701Enti/SEVETEST30/pattern/IMG20230719233832.jpg

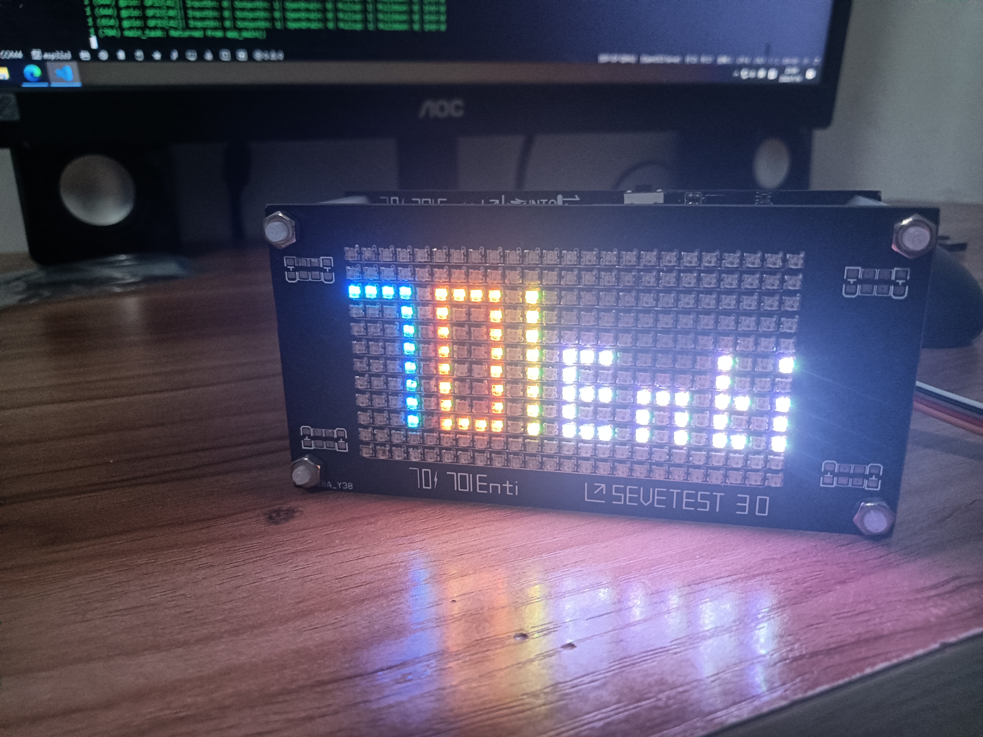
pattern/IMG20230719233832.jpg
