701Enti/SEVETEST30/pattern/sign/sign_sevetest30.png

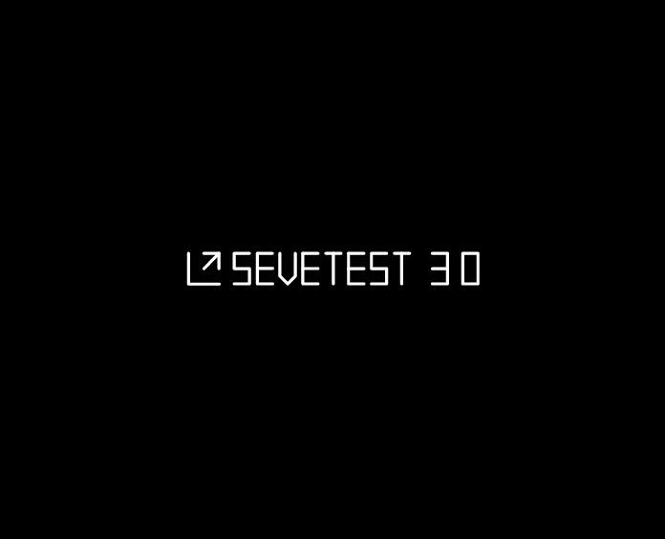
pattern/sign/sign_sevetest30.png
