701Enti/SEVETEST30/main/include/sevetest30_UI.h

/*
 * 701Enti MIT License
 *
 * Copyright © 2024 <701Enti organization>
 *
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
 * THE SOFTWARE IS PROVIDED “AS IS”, WITHOUT WARRANTY OF ANY KIND, EXPRESS OR
 * IMPLIED, INCLUDING BUT NOT LIMITED TO THE WARRANTIES OF MERCHANTABILITY,
 * FITNESS FOR A PARTICULAR PURPOSE AND NONINFRINGEMENT. IN NO EVENT SHALL THE
 * AUTHORS OR COPYRIGHT HOLDERS BE LIABLE FOR ANY CLAIM, DAMAGES OR OTHER
 * LIABILITY, WHETHER IN AN ACTION OF CONTRACT, TORT OR OTHERWISE, ARISING FROM,
 * OUT OF OR IN CONNECTION WITH THE SOFTWARE OR THE USE OR OTHER DEALINGS IN THE
 * SOFTWARE.
 */

// 包含对传感器数据，网络API等数据的 整理显示与动画交互工作
// 如您发现一些问题，请及时联系我们，我们非常感谢您的支持
// 敬告：该库自动调用 IWEDA库 SWEDA库 BWEDA库
// 读取数据，无需任何干涉，因此需要依赖一些库获取缓存变量，图像数据将只在文件函数内生效来节省内存，不会声明
// 显示UI根据sevetest30实际定制，特别是图像坐标，如果需要改变屏幕大小，建议自行设计修改
// github: https://github.com/701Enti

#pragma once

#include <driver/i2s.h>
#include <esp_err.h>
#include <stdbool.h>


// FFT相关
#define FFT_UI_TASK_CORE (0)              // FFT UI绘制任务核心
#define FFT_UI_TASK_STACK_SIZE (4 * 1024) // FFT UI绘制任务堆栈大小

#define FFT_N_SAMPLES 2048                       // FFT 点数N 取2的整数次幂
#define DSP_MAX_FFT_SIZE CONFIG_DSP_MAX_FFT_SIZE // 最大FFT缓冲区大小

#define FFT_VIEW_WIDTH_MAX 128 //// FFT UI视口宽度最大值

#define FFT_CURRENT_SOUND_BUF_WAIT_TIME_MS                                     \
  1000 // FFT读取当前音频缓冲区锁竞争超时，0表示不等待锁，单位ms

// 动画相关
#define CARTOON_PARAM_RENDER_PRECISION 10000 // 动画渲染参数计算精度
#define CARTOON_KEY_FRAME_PCT_MAX                                              \
  10000 // 动画关键帧百分位置标识的最大值 1标识动画开始一帧
        // [CARTOON_KEY_FRAME_PCT_MAX]标识最后一帧

typedef struct UI_color_visual_cfg_t {
  uint8_t value_max;  // 映射结果(RGB颜色数据)的最大值 0 - 255
  int high;           // 较高的值
  int medium;         // 中等的值
  int low;            // 较低的值
  int public_divisor; // 公共除数，抑制数据变化动态，过大过小都会出现全部填充value_max的情况，导致色彩单一,可从
                      // (high - low)/2 开始 调整到可视化动态效果最加即可
} UI_color_visual_cfg_t;

// 什么是视口
// 视口是指不受屏幕尺寸约束情况下的音频数据可视化区域，即对FFT原生输出图谱数据的处理得出
// 本质是将FFT原生输出图谱数据,根据视口参数,进行处理和映射,即将宽度为点数N的原生FFT数据,映射到宽度为视口宽度width的数据
// 每个单位宽度数据取对应原生FFT数据的最大值
// 你可以通过调整视口宽度和高度,以及视口横向缩放倍数和视口偏移系数,来改变视口显示效果
// 同时你可以通过改变屏幕打印使用的xy坐标,来改变屏幕从视口截取的图像位置
// 因此，你主要通过改变视口参数,来改变显示效果,不是控制屏幕显示,而是间接控制

// 注意:
// 1. 视口宽度大于LINE_LED_NUMBER会显示不完整视口
// 2. 视口高度大于VERTICAL_LED_NUMBER会显示不完整视口
// 3.
// 设置的视口参数对应视口位置如果超出FFT输出范围,会自动裁切超出部分,导致部分数据丢失

typedef struct music_FFT_UI_cfg_t {
  bool lr_switch; /// 选择显示左声道或右声道，0为左声道，1为右声道
  int16_t x;      /// 起始位置X坐标
  int16_t y;      /// 起始位置Y坐标
  UI_color_visual_cfg_t color_visual_cfg; // 频谱颜色可视化配置
  float x_multiples; // 视口横向缩放倍数(缩放原点为最低频点0),控制视口的横向放大缩小
                     // 缩小<1且大于0 放大>1 不进行=1 (如横向视口放大到200%
                     // x_multiples = 2)
  float x_move; // 视口偏移系数 左偏移<0 右偏移>0 不进行 0
                // (如把视口向右横向偏移视口宽度的一半 x_move = 0.5)
  int width; /// 视口宽度
             /// 图谱显示会按照设置参数适应视口宽度,如果你想显示完整视口,必须设置为等于或小于LINE_LED_NUMBER
  int height; /// 视口高度
              /// 如果你想显示完整视口,必须设置为等于或小于VERTICAL_LED_NUMBER
  int show_height_max; /// 显示图像的高度的最大值
                       /// 会裁切不在显示高度最大值范围内的图谱
  float dampen_multiples; /// 数据衰减倍数,必须大于0 >1表示衰减到原来1/2倍
                          /// <1表示放大到原来2倍
  float data_max; /// 衰减后数据的最大值 会裁切不在数据最大值范围内的图谱
  float data_min; /// 衰减后数据的最小值 会裁切不在数据最小值范围内的图谱
} music_FFT_UI_cfg_t;

#define FFT_UI_DEFAULT_CONFIG()                                                \
  {                                                                            \
      .x = 1,                                                                  \
      .y = 1,                                                                  \
      .lr_switch = 0,                                                          \
      .color_visual_cfg =                                                      \
          {                                                                    \
              .value_max = 255,                                                \
              .high = 4096,                                                    \
              .medium = (4096 - 0) / 2,                                        \
              .low = 0,                                                        \
              .public_divisor = (4096 - 0) / 2,                                \
          },                                                                   \
      .dampen_multiples = 50,                                                  \
      .data_max = 4096,                                                        \
      .data_min = 0,                                                           \
      .x_multiples = 5,                                                        \
      .x_move = 2.8,                                                           \
      .width = LINE_LED_NUMBER,                                                \
      .height = VERTICAL_LED_NUMBER,                                           \
      .show_height_max = VERTICAL_LED_NUMBER,                                  \
  }

typedef struct music_FFT_UI_t {
  music_FFT_UI_cfg_t cfg;
  bool volatile running_flag;
} music_FFT_UI_t;

typedef struct music_FFT_UI_t *music_FFT_UI_handle_t;

typedef struct cartoon_ctrl_param_t {
  int32_t x;        // x轴坐标
  int32_t y;        // y轴坐标
  uint8_t color[3]; // 颜色
} cartoon_ctrl_param_t;

// 控制对象
typedef struct cartoon_ctrl_object_t {
  uint32_t *pstep; // 显示函数自增的step步进值数据位置(可0),hook函数只读
  int32_t *px;     // 需要控制的x轴坐标数据位置,hook函数只写
  int32_t *py;     // 需要控制的y轴坐标数据位置,hook函数只写
  uint8_t *pcolor; // 需要控制的颜色数据位置,hook函数只写
} cartoon_ctrl_object_t;

// 动画关键帧属性选择
typedef enum {
  // 渲染关键帧
  KEY_FRAME_ATTR_LINEAR = 0, // 线性关键帧,线性地调整参量直到设置水平
  KEY_FRAME_ATTR_EASE_IN,    // 缓动关键帧-缓入
                          // 至少对应一个标记其前的拟合关键帧,否则被识别为线性关键帧
  KEY_FRAME_ATTR_EASE_OUT, // 缓动关键帧-缓出
                           // 至少对应一个标记其后的拟合关键帧,否则被识别为线性关键帧
  KEY_FRAME_ATTR_CONTINUOUS, // 连续关键帧,使用在两关键帧之间,保持这两关键帧最终效果但期间向连续关键帧偏移
  KEY_FRAME_ATTR_HOLD,    // 保持关键帧,开始保持设置的状态直到下一关键帧
  KEY_FRAME_ATTR_FITTING, // 拟合关键帧-创建在缓动关键帧周围(缓入之前,缓出之后)用于进一步拟合缓动参量变化函数,至少一个缓动关键帧对应一个,否则被识别为线性关键帧
                          // 非渲染关键帧
  KEY_FRAME_ATTR_STEGANOGRAPHY, // 隐写关键帧-参数不以key_frame_t规定格式填写,完全不参与渲染,占用关键帧数据库内存但数据不进参量表,以某种方式在动画生成callback时传递数据的伪造关键帧
} key_frame_attr_t;

// 隐写关键帧:参数不以key_frame_t规定格式填写,完全不参与渲染,占用关键帧数据库内存但数据不进参量表,以某种方式在动画生成callback时传递数据的伪造关键帧
// 隐写关键帧是动画支持工作下无函数快速操作数据,运行命令的一种方式,隐写关键帧的单位数据类型为key_frame_t,但是对应关系改变,如下
//  typedef struct key_frame_t {
//     key_frame_attr_t
//     frame_attribute;//关键帧属性,必须填写为KEY_FRAME_ATTR_STEGANOGRAPHY
//     int32_t percentage;//模式选择,取值[CARTOON_KEY_FRAME_PCT_MAX + 1] -
//     [CARTOON_KEY_FRAME_PCT_MAX + n],表示隐写操作的模式 int32_t
//     x;//[隐写数据位x - 4字节] int32_t y;//[隐写数据位y - 4字节] int32_t
//     color[3];//[隐写数据位color[0]color[1]color[2] - 每个4字节] int32_t
//     change;//[隐写数据位change - 4字节] int32_t
//     step_buf;//[隐写数据位step_buf - 4字节]
//  }key_frame_t;
// percentage参数的标定使得可以运行多种隐写模式,实现多种操作,隐写模式类型如下,枚举选择需要的隐写模式

typedef enum {
  // 隐写模式:映射 -
  // [警告:只有隐写关键帧设置在目标关键帧之后数据才能运行]映射内存中的数据以填充任意关键帧
  // x y color[3] change
  // 存储要读取的内存地址(为NULL的不读取),根据x(隐写数据位x)地址读到的数据根据映射关系映射到目标关键帧数据单元的x成员上,以此类推
  // step_buf不同,存储的是要映射到的对象关键帧在key_frame_database的角标
  STEGANOGRAPHY_MODE_MAPPING_EQUATION =
      CARTOON_KEY_FRAME_PCT_MAX +
      1, // 相等映射,映射关系为相等,源数据直接覆盖目标位置
  STEGANOGRAPHY_MODE_MAPPING_ADDITION, // 加法映射,覆盖目标位置的值为
                                       // [映射前目标位置的值 加上 源数据]
  STEGANOGRAPHY_MODE_MAPPING_SUBTRACTION, // 减法映射,覆盖目标位置的值为
                                          // [映射前目标位置的值 减去 源数据]
  STEGANOGRAPHY_MODE_MAPPING_MULTIPLICATION, // 乘法映射,覆盖目标位置的值为[映射前目标位置的值
                                             // 乘上 源数据]
  STEGANOGRAPHY_MODE_MAPPING_DIVISION, // 除法映射,覆盖目标位置的值为[映射前目标位置的值
                                       // 除以 源数据]
} steganography_mode_t; // 隐写操作模式类型

// 动画关键帧类型
typedef struct key_frame_t {
  key_frame_attr_t frame_attribute; // 关键帧属性
  int32_t
      percentage; // 关键帧百分位置,取值0-[CARTOON_KEY_FRAME_PCT_MAX],表示播放步数百分比(末两位数表示小数部分)
  int32_t step_buf; // 关键帧步位置缓存,该关键帧在第step步映射(可为0)
  int32_t x;        // x轴坐标
  int32_t y;        // y轴坐标
  int32_t color[3]; // 颜色
} key_frame_t;

// 动画计划类型
typedef struct cartoon_plan_t {
  key_frame_t *key_frame_database; // 动画计划关键帧数据库
  bool x_en;                       // 启用x轴坐标控制
  bool y_en;                       // 启用y轴坐标控制
  bool color_en;                   // 启用颜色控制
  uint32_t total_key_frame; // 实际总关键帧数缓存(私有缓存,用户函数请勿赋值)
  uint32_t total_step_buf;  // 实际总步数缓存(私有缓存,用户函数请勿赋值)
} cartoon_plan_t;

// 动画生成回调函数类型,根据动画计划转换为控制参量表格式
typedef void (*cartoon_create_callback_func_t)(int, int32_t);

// 动画控制钩子类型,用于控制和运用动画参量
typedef void (*cartoon_ctrl_hook_func_t)(int, cartoon_ctrl_object_t *);

typedef struct cartoon_support_t {
  cartoon_plan_t cartoon_plan; // 动画计划,需要提前设置
  cartoon_ctrl_param_t
      *ctrl_param_list; // 控制参量表,不同处理策略的控制参量表,钩子和回调都不一
  cartoon_create_callback_func_t
      create_callback; // 动画生成回调,不同处理策略的控制参量表,钩子和回调都不一
  cartoon_ctrl_hook_func_t
      ctrl_hook; // 动画控制的钩子函数,不同处理策略的控制参量表,钩子和回调都不一
} cartoon_support_t;

typedef cartoon_support_t *cartoon_handle_t;

typedef enum {
  CARTOON_RUN_MODE_PRE_RENDER =
      0, // 预渲染,在动画运行前保存每步图像到参量表,适合时长短且关键帧数量非常多的动画计划(比较消耗内存)
         // CARTOON_RUN_MODE_REAL_TIME_RENDER,
  // //(未开发)实时渲染,在动画运行时,钩子函数直接通过关键帧的数据实时渲染,适合简单常规的动画计划(动画运行时比较占用CPU)
} cartoon_run_mode_t;

// 数据可视化函数
void data_to_color(int data, UI_color_visual_cfg_t *visual_cfg, uint8_t *high,
                   uint8_t *comfort, uint8_t *low);

void temp_to_color(int temp, uint8_t value_max, uint8_t *high, uint8_t *comfort,
                   uint8_t *low);

// 动画支持适配函数-模式:预渲染

void _PRE_RENDER_create_callback(cartoon_handle_t handle, int32_t total_step);
void _PRE_RENDER_ctrl_hook(cartoon_handle_t handle,
                           cartoon_ctrl_object_t *object);

// 动画支持通用函数

cartoon_handle_t cartoon_new(cartoon_run_mode_t run_mode, bool en_x, bool en_y,
                             bool en_color, int key_frame_max);
void cartoon_delete(cartoon_handle_t handle);
uint32_t add_new_key_frame(cartoon_handle_t handle, key_frame_attr_t attr,
                           uint32_t pct, int32_t step, int32_t x, int32_t y,
                           uint8_t color[3]);

void facial_expression_show(int x, int y, char *lable);
void weather_icon_temperature(int x, int y);
void time_UI_h_m(int x, int y);
void time_UI_s(int x, int y);
void time_UI_h_m_s(int x, int y);
void battery_UI(int x, int y);

void show_701Enti_sign(int x, int y);
void show_se30_sign(int x, int y);
void show_wifi_connected(int x, int y);
void show_wifi_not_connected(int x, int y);

void music_FFT_UI_draw(music_FFT_UI_handle_t handle);

music_FFT_UI_handle_t music_FFT_UI_start(music_FFT_UI_cfg_t *UI_cfg,
                                         UBaseType_t priority);
esp_err_t music_FFT_UI_stop(music_FFT_UI_handle_t handle);

void ui_tool_hsv2rgb(float H, float S, float V, uint8_t color[3]);
