701Enti/SEVETEST30/main/sevetest30_gpio.c

/*
 * 701Enti MIT License
 *
 * Copyright © 2024 <701Enti organization>
 *
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
 * The above copyright notice and this permission notice shall be included in all copies or substantial portions of the Software.
 *
 * THE SOFTWARE IS PROVIDED “AS IS”, WITHOUT WARRANTY OF ANY KIND, EXPRESS OR IMPLIED,
 * INCLUDING BUT NOT LIMITED TO THE WARRANTIES OF MERCHANTABILITY, FITNESS FOR A PARTICULAR PURPOSE AND NONINFRINGEMENT.
 * IN NO EVENT SHALL THE AUTHORS OR COPYRIGHT HOLDERS BE LIABLE FOR ANY CLAIM, DAMAGES OR OTHER LIABILITY,
 * WHETHER IN AN ACTION OF CONTRACT, TORT OR OTHERWISE, ARISING FROM,
 * OUT OF OR IN CONNECTION WITH THE SOFTWARE OR THE USE OR OTHER DEALINGS IN THE SOFTWARE.
 */

// 包含一些sevetest30的GPIO配置工作(内部+扩展)，主要为了TCA6416A控制函数的解耦
// 如您发现一些问题，请及时联系我们，我们非常感谢您的支持
// 敬告：文件本体只针对sevetest30的硬件设计，该库代码中的配置是否合理会影响到设备能否正常运行，请谨慎修改
// github: https://github.com/701Enti

#include "sevetest30_gpio.h"
#include "board_def.h"
#include "esp_log.h"
#include "esp_check.h"
#include "freertos/FreeRTOS.h"
#include "freertos/task.h"
#include "freertos/queue.h"
#include "driver/gpio.h"
#include "driver/uart.h"

ext_io_ctrl_t ext_io_ctrl = {
    .auto_read_EN = true,   // 使能自动读取,读取由外部程序监控auto_read_INT并调用读取函数实现
    .auto_read_INT = false, // true表示INT中断信号触发,外部调用读取函数成功读取后需自行复位到true
};

static TCA6416A_mode_t *P_ext_io_mode_data = NULL;   // 扩展IO输入输出模式
static TCA6416A_level_t *P_ext_io_value_data = NULL; // 扩展IO电平信息，写入和回读通用

// 中断参数传flag地址以保证flag值同步，该变量存储了这个地址，作为ISR参数
uint32_t P_ext_io_auto_read_flag;

static xQueueHandle ext_io_int_queue = NULL;

static void IRAM_ATTR ext_io_int_isr_handler(void *arg)
{
  uint32_t P_auto_read_flag = (uint32_t)arg;
  xQueueSendFromISR(ext_io_int_queue, &P_auto_read_flag, NULL);
}

static void ext_io_int_task(void *arg)
{
  bool flag_buf = true;
  uint32_t P_auto_read_flag;
  while (1)
  {
    vTaskDelay(pdMS_TO_TICKS(10));
    if (xQueueReceive(ext_io_int_queue, &P_auto_read_flag, portMAX_DELAY))
    {
      // 将自动读取标志值的地址作为ISR参数进行传输
      flag_buf = *(bool *)P_auto_read_flag;
      if (flag_buf)
      {
        vTaskDelay(pdMS_TO_TICKS(100));
        gpio_get_level(TCA6416A_INT_IO);
        if (gpio_get_level(TCA6416A_INT_IO) == 0)
        {
          ext_io_ctrl.auto_read_INT = true;
        }
      }
    }
  }
}

/// @brief 扩展GPIO电平值服务，读写通用，当有电平变化，系统中断触发会自动调用该函数，所以主要用来写操作
/// @brief 写：先对ext_io_value_data这个全局公共结构体变量修改值，等待系统大循环调用该函数写入IO电平
/// @brief 读：（当中断读取使能，只要电平变化系统中断触发，将全自动读取，一般无需调用）如果需要主动读取：先调用该函数刷新ext_io_value_data，之后直接读取ext_io_value_data内的成员变量值 */
/// @return [ESP_OK 成功]
/// @return [ESP_ERR_INVALID_ARG 参数错误]
/// @return [ESP_FAIL 发送命令时发现问题, TCA6416A未应答]
/// @return [ESP_ERR_INVALID_STATE I2C driver 未安装或没有运行在主机模式]
/// @return [ESP_ERR_TIMEOUT 操作超时因为总线忙]
esp_err_t ext_io_level_service()
{
  return TCA6416A_gpio_level_service(P_ext_io_value_data, P_ext_io_mode_data);
}

/// @brief 扩展GPIO输入输出模式服务
/// @brief 写：先对ext_io_mode_data这个全局公共结构体变量写入需要修改的值，再调用该函数控制IO输入输出模式
/// @brief 读：直接读取ext_io_mode_data内的成员变量值，不需要调用该函数 */
/// @return [ESP_OK 成功]
/// @return [ESP_ERR_INVALID_ARG 参数错误]
/// @return [ESP_FAIL 发送命令时发现问题, TCA6416A未应答]
/// @return [ESP_ERR_INVALID_STATE I2C driver 未安装或没有运行在主机模式]
/// @return [ESP_ERR_TIMEOUT 操作超时因为总线忙]
esp_err_t ext_io_mode_service()
{
  // 在将外部IO模式由输出模式转向输入模式时，可能发生意外中断问题，通过flag在模式设置时屏蔽中断自动读取，可以代价较低地避免可能性极小的重复读取问题的发生
  ext_io_ctrl.auto_read_EN = false;
  esp_err_t ret = TCA6416A_gpio_mode_set(P_ext_io_mode_data);
  ext_io_ctrl.auto_read_EN = true;
  return ret;
}

/// @brief 扩展GPIO(TCA6416A)重置到默认，在gpio_init函数调用时该函数就会被执行
/// @param p_mode 缓存位置-模式配置(比如定义一个TCA6416A_mode_t结构体作为缓存位置导入,之后可直接改变结构体成员值来控制扩展IO)
/// @param p_level 缓存位置-电平数据(比如定义一个TCA6416A_level_t结构体作为缓存位置导入,之后可直接改变结构体成员值来控制扩展IO)
/// @return [ESP_OK 成功]
/// @return [ESP_ERR_INVALID_ARG 参数错误]
/// @return [ESP_FAIL 发送命令时发现问题, TCA6416A未应答]
/// @return [ESP_ERR_INVALID_STATE I2C driver 未安装或没有运行在主机模式]
/// @return [ESP_ERR_TIMEOUT 操作超时因为总线忙]
esp_err_t ext_io_reset_to_default(TCA6416A_mode_t *p_mode, TCA6416A_level_t *p_level)
{
  const char *TAG = "ext_io_reset_to_default";

  TCA6416A_mode_t mode_buf = TCA6416A_DEFAULT_CONFIG_MODE;
  TCA6416A_level_t value_buf = TCA6416A_DEFAULT_CONFIG_VALUE;

  *p_mode = mode_buf;
  *p_level = value_buf;
  P_ext_io_mode_data = p_mode;
  P_ext_io_value_data = p_level;

  esp_err_t ret = ESP_OK;

  ret = TCA6416A_gpio_global_inversion_set(false);
  ESP_RETURN_ON_ERROR(ret, TAG, "重置扩展GPIO引脚极性反转配置到默认时发现问题");

  ret = ext_io_level_service();
  ESP_RETURN_ON_ERROR(ret, TAG, "重置扩展GPIO引脚电平到默认时发现问题");

  ret = ext_io_mode_service();
  ESP_RETURN_ON_ERROR(ret, TAG, "重置扩展GPIO引脚模式到默认时发现问题");  

  ESP_LOGI(TAG, "扩展GPIO重置成功");
  return ESP_OK;
}

/// @brief 全局GPIO初始化,包括内部IO和扩展IO
/// @param p_mode 缓存位置-模式配置(比如定义一个TCA6416A_mode_t结构体作为缓存位置导入,之后可直接改变结构体成员值来控制扩展IO)
/// @param p_level 缓存位置-电平数据(比如定义一个TCA6416A_level_t结构体作为缓存位置导入,之后可直接改变结构体成员值来控制扩展IO)
/// @return [ESP_OK 成功]
/// @return [ESP_ERR_INVALID_ARG 输入参数错误 / 选择了错误的GPIO]
/// @return [ESP_FAIL 发送命令时发现问题, TCA6416A未应答]
/// @return [ESP_ERR_INVALID_STATE ISR服务已经安装 / ISR服务安装失败 /  I2C driver 未安装或没有运行在主机模式]
/// @return [ESP_ERR_TIMEOUT 操作超时因为总线忙]
/// @return [ESP_ERR_NO_MEM 安装ISR服务时发现内存不足]
/// @return [ESP_ERR_NOT_FOUND 没有找到特定FLAG的空闲interrupt]
esp_err_t sevetest30_gpio_init(TCA6416A_mode_t *p_ext_mode, TCA6416A_level_t *p_ext_value)
{
  const char *TAG = "sevetest30_gpio_init";
  esp_err_t ret = ESP_OK;


  //释放UART0的GPIO连接
  uart_driver_delete(UART_NUM_0);
  uart_set_pin(UART_NUM_0,GPIO_NUM_NC,GPIO_NUM_NC,GPIO_NUM_NC,GPIO_NUM_NC);
  

  // // TCA6416A的RESET信号GPIO
  // gpio_config_t TCA6416A_reset_config = {
  //     .pin_bit_mask = 1ULL << TCA6416A_IO_RESET,
  //     .mode = GPIO_MODE_OUTPUT,
  //     .pull_up_en = GPIO_PULLUP_DISABLE,
  //     .pull_down_en = GPIO_PULLDOWN_DISABLE,
  //     .intr_type = GPIO_INTR_DISABLE,
  // };
  // ret = gpio_config(&TCA6416A_reset_config); // 配置GPIO
  // ESP_RETURN_ON_ERROR(ret, TAG, "配置TCA6416A的RESET信号GPIO时发现问题");
  // ret = gpio_set_level(TCA6416A_IO_RESET, 1); // 设置GPIO初始电平
  // ESP_RETURN_ON_ERROR(ret, TAG, "设置TCA6416A的RESET信号GPIO初始电平时发现问题");

  // TCA6416A的INT信号GPIO
  gpio_config_t TCA6416A_int_config = {
      .pin_bit_mask = 1ULL << TCA6416A_INT_IO,
      .mode = GPIO_MODE_INPUT,
      .pull_up_en = GPIO_PULLUP_DISABLE,
      .pull_down_en = GPIO_PULLDOWN_DISABLE,
      .intr_type = GPIO_INTR_NEGEDGE,
  };
  ret = gpio_config(&TCA6416A_int_config); // 配置GPIO
  ESP_RETURN_ON_ERROR(ret, TAG, "配置TCA6416A的INT信号GPIO时发现问题");

  // INT中断配置
  ext_io_int_queue = xQueueCreate(10, sizeof(uint32_t));                                                                       // 队列创建
  xTaskCreatePinnedToCore(ext_io_int_task, "ext_io_int_task", 2048, NULL, EXT_IO_READ_EVT_PRIO, NULL, EXT_IO_READ_EVT_CORE); // 中断识别任务创建
  ret = gpio_install_isr_service(EXT_IO_READ_INTR_FLAG);                                                                         // 安装GPIO ISR服务
  ESP_RETURN_ON_ERROR(ret, TAG, "安装TCA6416A的INT信号GPIO的ISR服务时发现问题");
  P_ext_io_auto_read_flag = (uint32_t)&ext_io_ctrl.auto_read_EN;                                                    // 将自动读取标志值的地址作为ISR参数进行传输
  ret = gpio_isr_handler_add(TCA6416A_INT_IO, ext_io_int_isr_handler, (void *)P_ext_io_auto_read_flag); // 为选定的GPIO添加ISR句柄
  ESP_RETURN_ON_ERROR(ret, TAG, "添加TCA6416A的INT信号GPIO的ISR句柄时发现问题");

  ret = ext_io_reset_to_default(p_ext_mode, p_ext_value); // 扩展gpio初始化
  ESP_RETURN_ON_ERROR(ret, TAG, "扩展GPIO重置到默认时发现问题");

  return ESP_OK;
}
