701Enti/SEVETEST30/main/default_UI_icon_data.c

/*
 * 701Enti MIT License
 *
 * Copyright © 2024 <701Enti organization>
 *
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
 * THE SOFTWARE IS PROVIDED “AS IS”, WITHOUT WARRANTY OF ANY KIND, EXPRESS OR
 * IMPLIED, INCLUDING BUT NOT LIMITED TO THE WARRANTIES OF MERCHANTABILITY,
 * FITNESS FOR A PARTICULAR PURPOSE AND NONINFRINGEMENT. IN NO EVENT SHALL THE
 * AUTHORS OR COPYRIGHT HOLDERS BE LIABLE FOR ANY CLAIM, DAMAGES OR OTHER
 * LIABILITY, WHETHER IN AN ACTION OF CONTRACT, TORT OR OTHERWISE, ARISING FROM,
 * OUT OF OR IN CONNECTION WITH THE SOFTWARE OR THE USE OR OTHER DEALINGS IN THE
 * SOFTWARE.
 */

// 默认图标库
// 如您发现一些问题，请及时联系我们，我们非常感谢您的支持
// github: https://github.com/701Enti

#include "default_UI_icon_data.h"
#include <string.h>

///@brief 获取天气图标数据
///@param icon_data 图标数据指针
///@param index_id 图标索引ID
///@return -1 失败，否则返回天气事件正在进行标识，1 表示正在进行天气事件，0
/// 表示未正在进行天气事件
int get_weather_icon_data(unsigned char icon_data[251], int index_id) {
  if (icon_data == NULL) {
    return -1;
  }
  memset(icon_data, 0, 251);

  const unsigned char *ptr = NULL;
  int weather_change_flag = 0;
  switch (index_id) {
    // 正在进行的
  case 100: {
    ptr = weather_icon_100;
    break;
  }
  case 101: {
    ptr = weather_icon_101;
    break;
  }
  case 102: {
    ptr = weather_icon_102;
    break;
  }
  case 103: {
    ptr = weather_icon_103;
    break;
  }
  case 104: {
    ptr = weather_icon_104;
    break;
  }
  case 150: {
    ptr = weather_icon_150;
    break;
  }
  case 151: {
    ptr = weather_icon_151;
    break;
  }
  case 152: {
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
    0X00, 0X00, 0X00, 0X00, 0X00, 0X00, 0X00, 0X00, 0X00, 0X00, 0X00, 0X00,
    0X00, 0X00, 0X00, 0X00, 0X00, 0X00, 0X00, 0X00, 0X00, 0X00, 0X00, 0X00,
    0X00, 0X00, 0X00, 0X00, 0X00, 0X00, 0X00, 0X00, 0X00, 0X00, 0X00, 0X00,
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
};
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
