701Enti/SEVETEST30/main/math_tools.c

/*
 * 701Enti MIT License
 *
 * Copyright © 2025 <701Enti organization>
 *
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
 * The above copyright notice and this permission notice shall be included in all copies or substantial portions of the Software.
 *
 * THE SOFTWARE IS PROVIDED “AS IS”, WITHOUT WARRANTY OF ANY KIND, EXPRESS OR IMPLIED,
 * INCLUDING BUT NOT LIMITED TO THE WARRANTIES OF MERCHANTABILITY, FITNESS FOR A PARTICULAR PURPOSE AND NONINFRINGEMENT.
 * IN NO EVENT SHALL THE AUTHORS OR COPYRIGHT HOLDERS BE LIABLE FOR ANY CLAIM, DAMAGES OR OTHER LIABILITY,
 * WHETHER IN AN ACTION OF CONTRACT, TORT OR OTHERWISE, ARISING FROM,
 * OUT OF OR IN CONNECTION WITH THE SOFTWARE OR THE USE OR OTHER DEALINGS IN THE SOFTWARE.
 */

 // 包含各种基于ESP-DSP的数学工具函数
 // 如您发现一些问题，请及时联系我们，我们非常感谢您的支持
 // github: https://github.com/701Enti
 
#include "math_tools.h"
#include "esp_err.h"
#include "esp_check.h"
#include "esp_log.h"
#include "esp_dsp.h"
#include "esp_cpu.h"
#include <stdbool.h>
#include <string.h>
#include <math.h>


static const char* math_tools_TAG = __FILE__;

/// @brief 通用矩阵转置
/// @param input 矩阵输入 
/// @param output 矩阵输出
/// @param m 原矩阵的行数
/// @param n 原矩阵的列数
void general_matrix_transpose(float* input, float* output, int m, int n) {
    for (int i = 0;i < m;i++) {
        for (int j = 0;j < n;j++) {
            //input(共m行,n列) 第i行,第j列 为 output(共n行,m列) 第j行,第i列的值
            output[j * m + i] = input[i * n + j];
        }
    }
}

void aligned_16_matrix_transpose(float* input, float* output, int m, int n) {

}

/// @brief 方阵原地转置,直接在输入上操作
/// @param local 矩阵输入 
/// @param n 原矩阵(n,n)的列数
void square_matrix_inplace_transpose(float* local, int n) {
    for (int i = 0;i < n;i++) {
        for (int j = i + 1;j < n;j++) {//仅遍历上三角
            float buf = local[i * n + j];
            local[i * n + j] = local[j * n + i];
            local[j * n + i] = buf;
        }
    }
}




void square_aligned_16_matrix_transpose(float* local, int n) {

}

/// @brief [目前仅支持行主序]矩阵转置,自动根据上下文参数选择更优更快的处理方式(如何触发见下方备注),若满足多个优化条件,优化可能叠加 (一般不会修改源数据矩阵,除非方阵触发原地转置优化)
/// @note [触发-内存16对齐优化]通过一些方式,在申请内存后获得16对齐内存(可获得更快的速度)
/// @note [触发-方阵优化(前提是运算对象是方阵)](会修改源数据矩阵)使得 m = n , input == output , input != NULL , output != NULL 同时满足,即输入输出都是一个内存区域(可实现原地转置,减少内存消耗)
/// @param input 矩阵输入 
/// @param output 矩阵输出
/// @param m 原矩阵的行数
/// @param n 原矩阵的列数
/// @return [ESP_OK 运算完成]  
/// @return [ESP_ERR_INVALID_ARG input为NULL / output为NULL / m <= 0 / n <= 0] 
esp_err_t matrix_transpose(float* input, float* output, int m, int n) {
    //参数检查
    ESP_RETURN_ON_FALSE(input && output && m > 0 && n > 0, ESP_ERR_INVALID_ARG, math_tools_TAG, "传入参数异常 描述%s", esp_err_to_name(ESP_ERR_INVALID_ARG));

    // //选出最佳策略
    // if ((uintptr_t)input % 16 == 0 && (uintptr_t)output % 16 == 0) {
    //     //input output 16内存对齐
    //     if (input == output) {
    //         //在同一内存区域操作 + input output 16内存对齐
    //         if (m == n) {
    //             //[触发-方阵优化]+[触发-内存16对齐优化] <- 方阵 + 在同一内存区域操作 + input output 16内存对齐
    //             square_aligned_16_matrix_transpose(input, n);
    //             return ESP_OK;
    //         }
    //     }

    //     //在上方如果未获得更优策略,就不会return,从而执行下方策略
    //     aligned_16_matrix_transpose(input, output, m, n);
    //     return ESP_OK;
    // }
    // else {
    //     if (input == output) {
    //         //在同一内存区域操作
    //         if (m == n) {
    //             //[触发-方阵优化] <- 方阵 + 在同一内存区域操作
    //             square_matrix_inplace_transpose(input, n);
    //             return ESP_OK;
    //         }
    //     }

        //在上方如果未获得更优策略,就不会return,从而执行下方策略
    general_matrix_transpose(input, output, m, n);
    return ESP_OK;
    // }

    //请勿在本函数末尾添加return语句
    //请勿在本函数末尾添加return语句
    //请勿在本函数末尾添加return语句
    //编译器根据if中的return自动检查if逻辑,请勿在本函数末尾添加return语句,报错说明if逻辑异常,或未在本次更改新添加的策略函数调用下方紧接着return ESP_OK;
}



/// @brief [目前仅支持行主序]获取矩阵中目标列的主元的行号(找出矩阵目标列中的主元位置,输出它的行号)(不会修改源数据矩阵)
/// @param A 需要进行查找操作的矩阵A(m x n)
/// @param m 矩阵A的总行数
/// @param n 矩阵A的总列数
/// @param aim_col 目标列(列号,范围 0 - n-1)
/// @param start_row [优化参数]要求从行号(范围 0 - m-1)为start_row的行开始向下查找,不需要填写0即可(整列数全部参与查找)
/// @return 目标列中的主元的行号(范围 0 - m-1)
int matrix_get_the_row_of_aim_col_pivot(const float* A, int m, int n, int aim_col, int start_row) {
    int ret = start_row;//返回值缓存
    float max = 0;//当前发现的最大绝对值
    float a = 0;//当前位置元素绝对值缓存
    for (int r = start_row;r < m;r++) {//r为当前遍历的行号
        //主元即绝对值最大
        a = fabsf(A[r * n + aim_col]);//当前位置元素绝对值
        if (a > max) {
            max = a;
            ret = r;
        }
    }
    return ret;
}

/// @brief [目前仅支持行主序](会修改源数据矩阵)矩阵中的两行(r1和r2)交换所有元素
/// @param A 需要进行交换操作的矩阵A(m x n)
/// @param n 矩阵A的总列数
/// @param r1 需要进行交换操作的行号(范围 0 - m-1)
/// @param r2 需要进行交换操作的行号(范围 0 - m-1)
void matrix_swap_rows(float* A, int n, int r1, int r2) {
    if (r1 == r2) {
        return;
    }
    else {
        float buf = 0;//元素值缓存
        for (int c = 0;c < n;c++) {
            buf = A[r1 * n + c];
            A[r1 * n + c] = A[r2 * n + c];
            A[r2 * n + c] = buf;
        }
        return;
    }
}

/// @brief [目前仅支持行主序](会修改源数据矩阵)矩阵中的两行(r1和r2)交换所有元素,但是其中列号大于等于k的列不进行任何交换操作
/// @param A 需要进行交换操作的矩阵A(m x n)
/// @param n 矩阵A的总列数
/// @param r1 需要进行交换操作的行号(范围 0 - m-1)
/// @param r2 需要进行交换操作的行号(范围 0 - m-1)
/// @param k 交换列范围限制,列号大于等于k的列不进行任何交换操作
void matrix_swap_rows_with_col_limit(float* A, int n, int r1, int r2, int k) {
    if (r1 == r2) {
        return;
    }
    else {
        float buf = 0;//元素值缓存
        for (int c = 0;c < k;c++) {
            buf = A[r1 * n + c];
            A[r1 * n + c] = A[r2 * n + c];
            A[r2 * n + c] = buf;
        }
        return;
    }
}
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
